ccadic/NewMorphS3/invader-a-la-generale (1).jpg

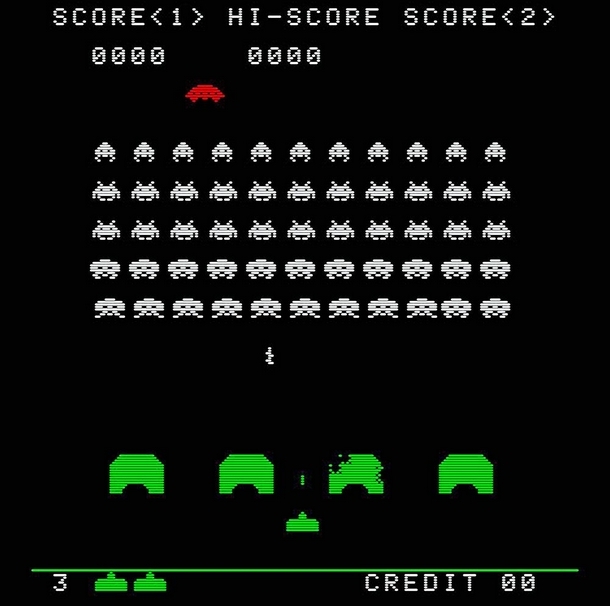
invader-a-la-generale (1).jpg
