ccadic/NewMorphS3/JOYSP3.jpg

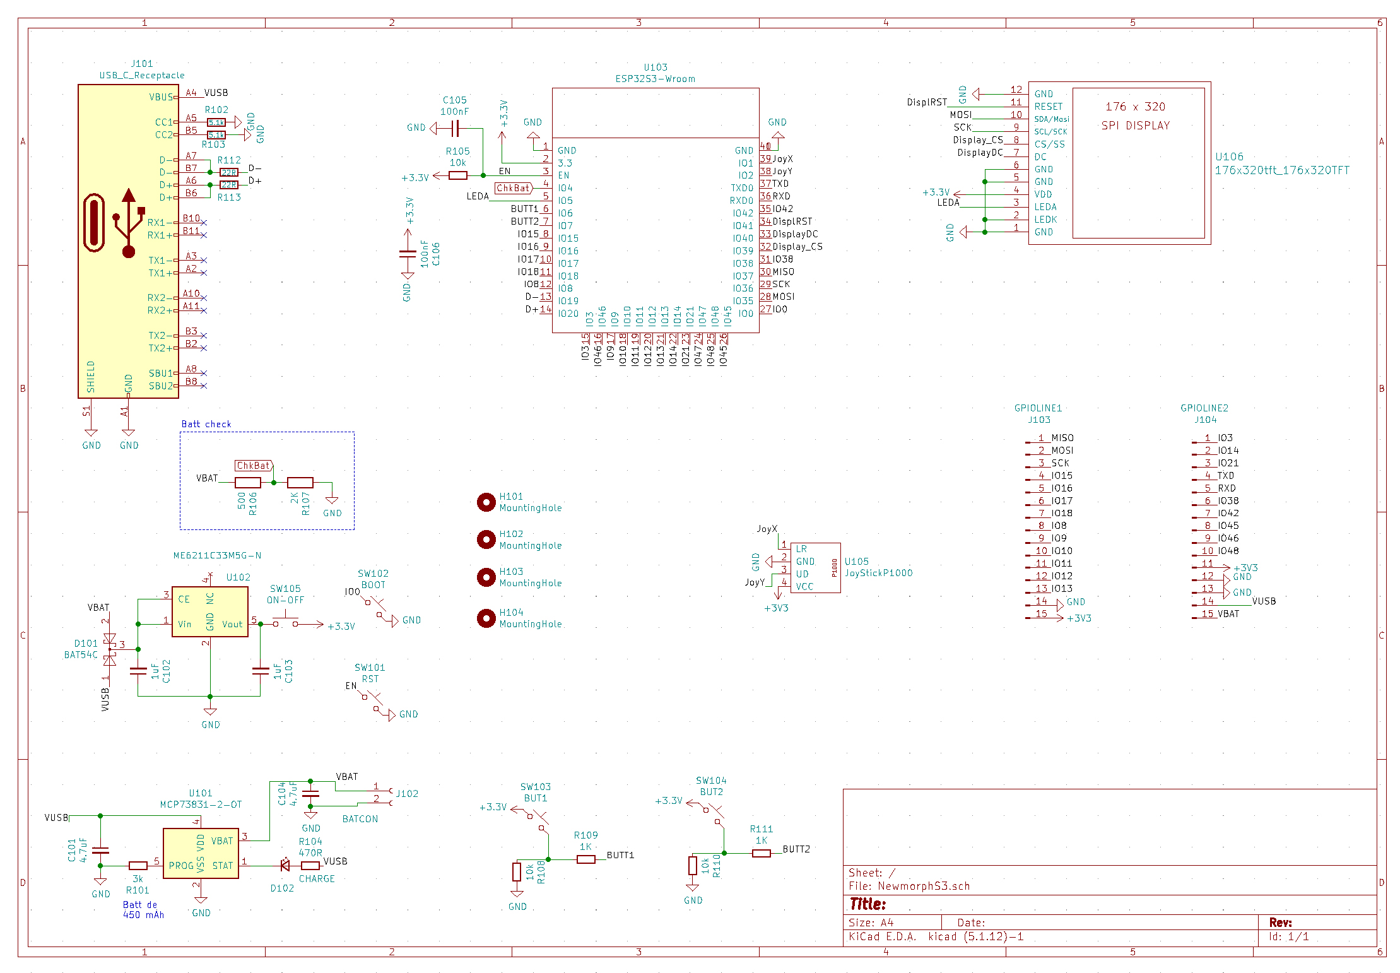
JOYSP3.jpg
