ccadic/NewMorphS3/MicroSDNewmorphS3.jpg

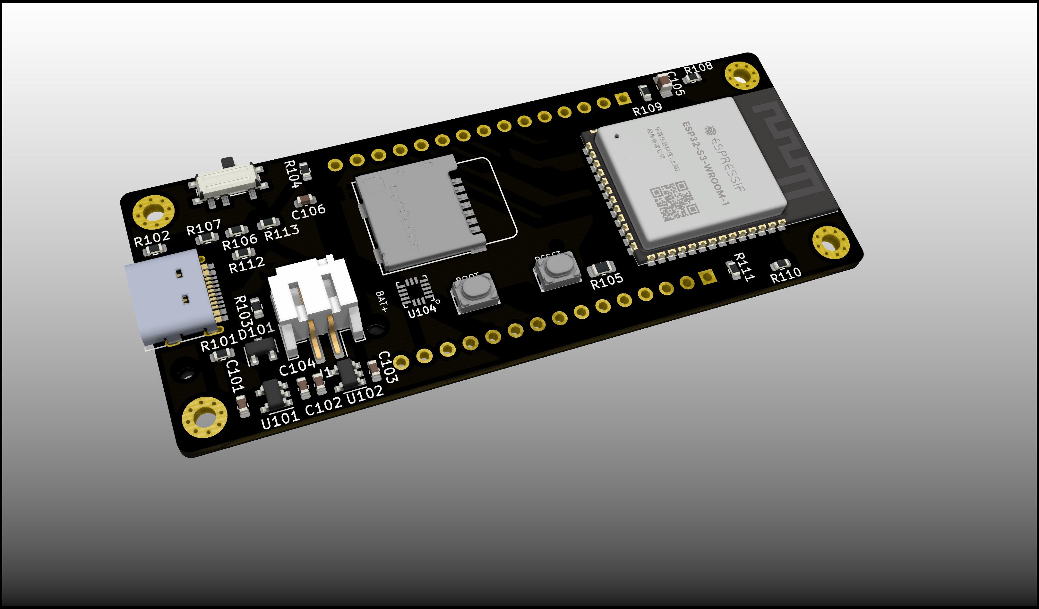
MicroSDNewmorphS3.jpg
