ccadic/NewMorphS3/NewmorphS3beta1.jpg

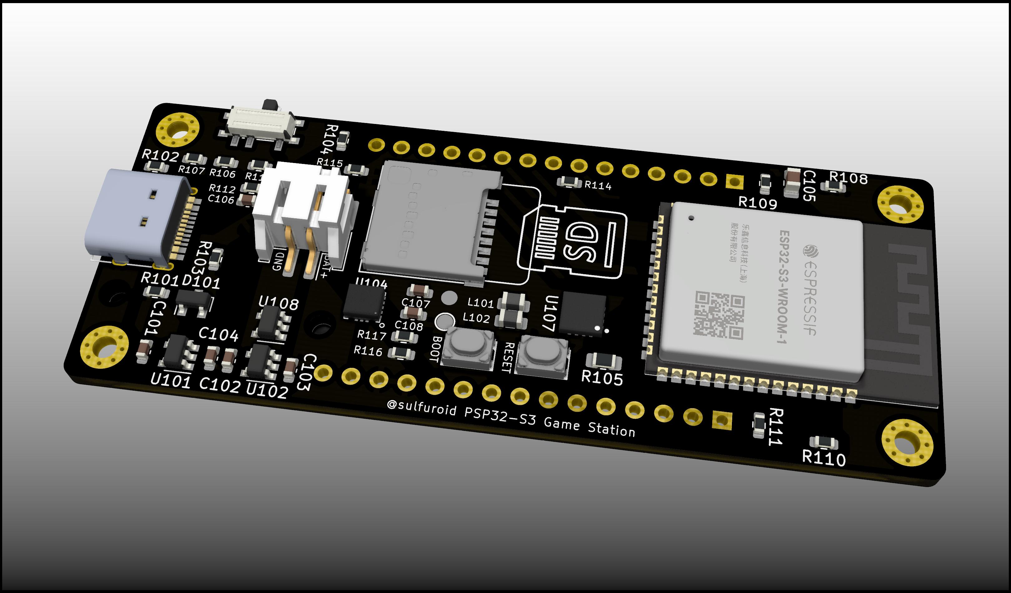
NewmorphS3beta1.jpg
