ccadic/NewMorphS3/NewmorphS3C.jpg

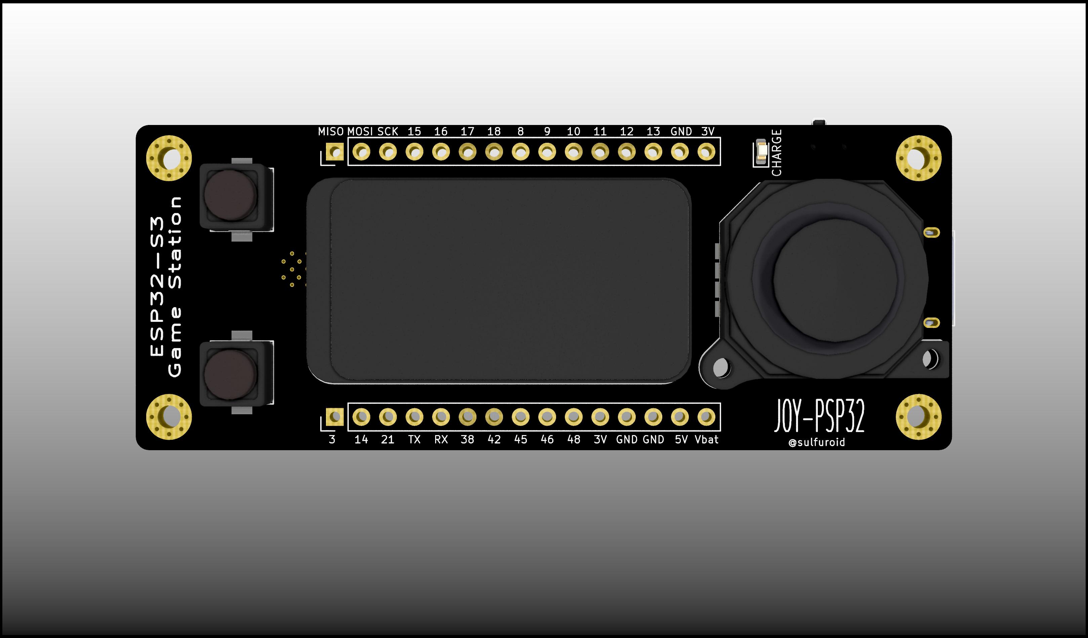
NewmorphS3C.jpg
