ccadic/NewMorphS3/sdwiring.jpg

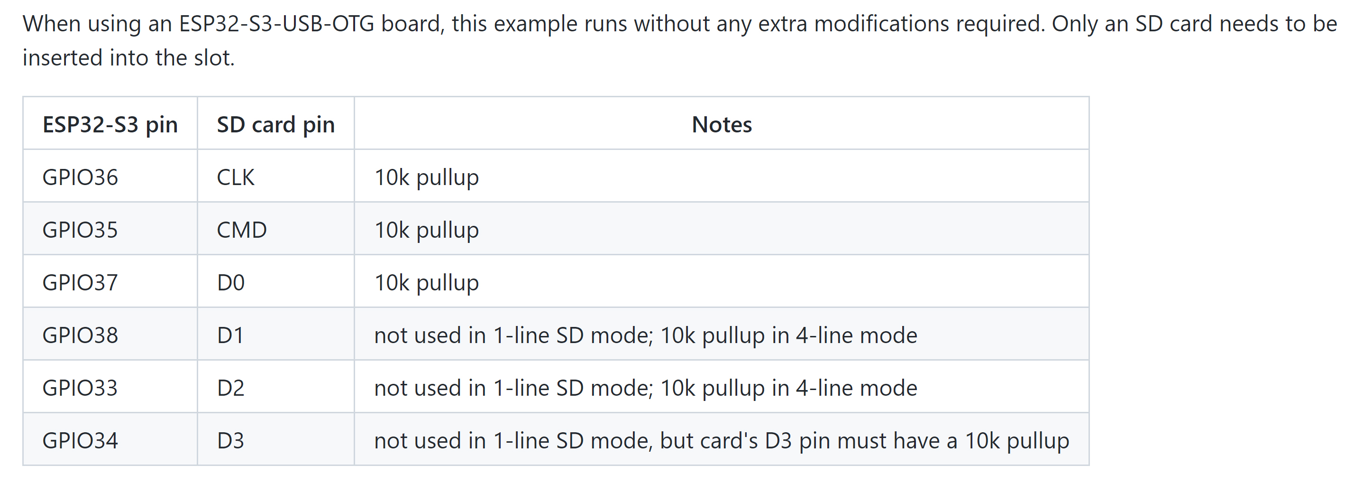
sdwiring.jpg
